daid/ArcadeElectronics/Software/computer/gui_test/gui.cpp

#include <SDL/SDL.h>

SDL_Surface *screen;

static const uint8_t font[] = {
    0x00, 0x00, 0x00, 0x00, 0x00,// (space)
	0x00, 0x00, 0x5F, 0x00, 0x00,// !
	0x00, 0x07, 0x00, 0x07, 0x00,// "
	0x14, 0x7F, 0x14, 0x7F, 0x14,// #
	0x24, 0x2A, 0x7F, 0x2A, 0x12,// $
	0x23, 0x13, 0x08, 0x64, 0x62,// %
	0x36, 0x49, 0x55, 0x22, 0x50,// &
	0x00, 0x05, 0x03, 0x00, 0x00,// '
	0x00, 0x1C, 0x22, 0x41, 0x00,// (
	0x00, 0x41, 0x22, 0x1C, 0x00,// )
	0x08, 0x2A, 0x1C, 0x2A, 0x08,// *
	0x08, 0x08, 0x3E, 0x08, 0x08,// +
	0x00, 0x50, 0x30, 0x00, 0x00,// ,
	0x08, 0x08, 0x08, 0x08, 0x08,// -
	0x00, 0x60, 0x60, 0x00, 0x00,// .
	0x20, 0x10, 0x08, 0x04, 0x02,// /
	0x3E, 0x51, 0x49, 0x45, 0x3E,// 0
	0x00, 0x42, 0x7F, 0x40, 0x00,// 1
	0x42, 0x61, 0x51, 0x49, 0x46,// 2
	0x21, 0x41, 0x45, 0x4B, 0x31,// 3
	0x18, 0x14, 0x12, 0x7F, 0x10,// 4
	0x27, 0x45, 0x45, 0x45, 0x39,// 5
	0x3C, 0x4A, 0x49, 0x49, 0x30,// 6
	0x01, 0x71, 0x09, 0x05, 0x03,// 7
	0x36, 0x49, 0x49, 0x49, 0x36,// 8
	0x06, 0x49, 0x49, 0x29, 0x1E,// 9
	0x00, 0x36, 0x36, 0x00, 0x00,// :
	0x00, 0x56, 0x36, 0x00, 0x00,// ;
	0x00, 0x08, 0x14, 0x22, 0x41,// <
	0x14, 0x14, 0x14, 0x14, 0x14,// =
	0x41, 0x22, 0x14, 0x08, 0x00,// >
	0x02, 0x01, 0x51, 0x09, 0x06,// ?
	0x32, 0x49, 0x79, 0x41, 0x3E,// @
	0x7E, 0x11, 0x11, 0x11, 0x7E,// A
	0x7F, 0x49, 0x49, 0x49, 0x36,// B
	0x3E, 0x41, 0x41, 0x41, 0x22,// C
	0x7F, 0x41, 0x41, 0x22, 0x1C,// D
	0x7F, 0x49, 0x49, 0x49, 0x41,// E
	0x7F, 0x09, 0x09, 0x01, 0x01,// F
	0x3E, 0x41, 0x41, 0x51, 0x32,// G
	0x7F, 0x08, 0x08, 0x08, 0x7F,// H
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
};

void init_gui()
{
    if ( SDL_Init(SDL_INIT_EVERYTHING) < 0 ) 
    {
        fprintf(stderr, "Unable to init SDL: %s\n", SDL_GetError());
        exit(1);
    }
    atexit(SDL_Quit);
    
    screen = SDL_SetVideoMode(640, 480, 32, SDL_SWSURFACE);
}

void draw_text(int x, int y, const char* str, int color = 0xFFFFFF)
{
    SDL_LockSurface(screen);
    uint32_t* pix = ((uint32_t*)screen->pixels) + screen->pitch / 4 * y + x;
    for(char c = *str++; c; c = *str++)
    {
        const uint8_t* f = &font[(c-' ')*5];
        
        for(int _x=0; _x<5;_x++)
        {
            for(int n=0; n<7;n++)
            {
                if (*f & (1 << n))
                    pix[n * screen->pitch/4] = color;
            }
            pix++;
            f++;
        }
        pix++;
    }
    SDL_UnlockSurface(screen);
}

void draw_fill(int x, int y, int w, int h)
{
    SDL_Rect rect;
    rect.x = x;
    rect.y = y;
    rect.w = w;
    rect.h = h;
    
    SDL_FillRect(screen, &rect, 0xFFFFFF);
}

void draw_rect(int x, int y, int w, int h)
{
    draw_fill(x, y, 1, h);
    draw_fill(x, y, w, 1);
    draw_fill(x + w - 1, y, 1, h);
    draw_fill(x, y + h - 1, w, 1);
}

void gui_update()
{
    SDL_Flip(screen);
    SDL_FillRect(screen, NULL, 0x000000);
    SDL_Delay(20);
}
